francodichiera/dichiera-CartelLED/assets/ESP32+TIPS122 VERSION 3 TESTING/ESP32+TIPS/ESP32+TIPS (1).kicad_sch

## KiCad design assets/ESP32+TIPS122 VERSION 3 TESTING/ESP32+TIPS/ESP32+TIPS (1).kicad_sch (2025-08-08)

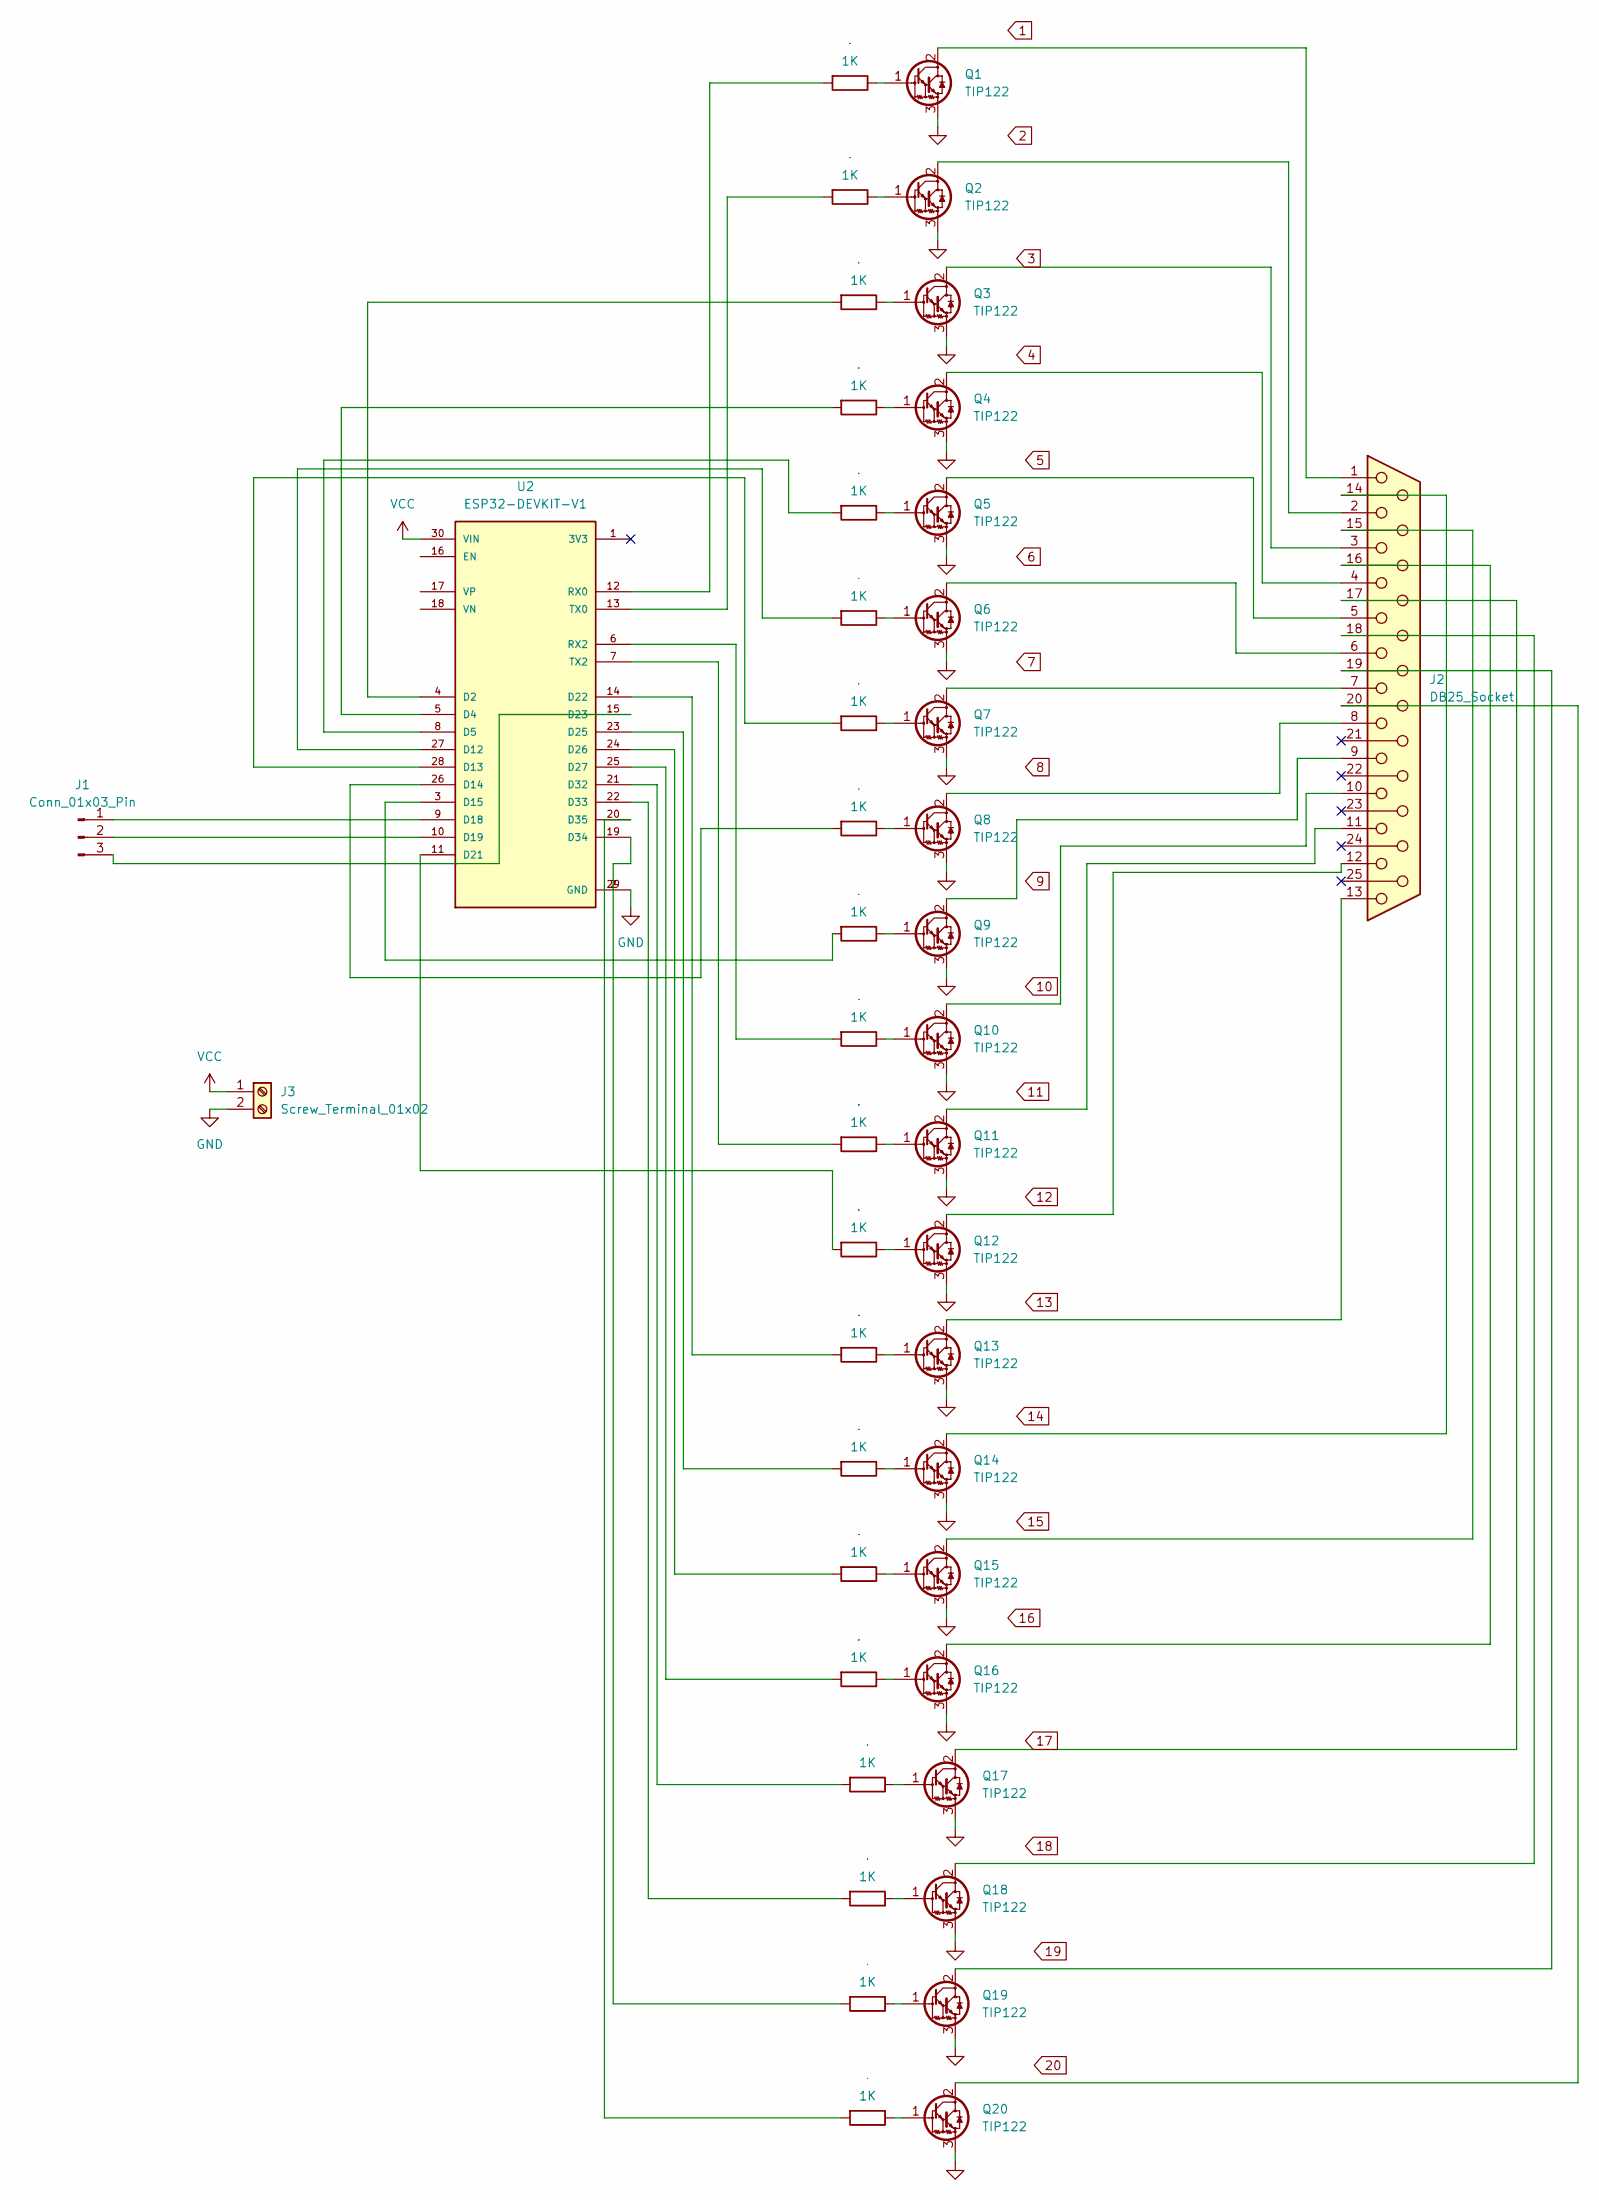
[picture p16: schematic ESP32+TIPS (1).kicad_sch]

Parts:
.1, .2, .3, .4, .5, .6, .7, .8, .9, .10, .11, .12, .13, .14, .15, .16, .17, .18, .19, .20: 1K; R_Axial_DIN0309_L9.0mm_D3.2mm_P20.32mm_Horizontal
J1: Conn_01x03_Pin; PinSocket_1x03_P2.54mm_Vertical
J2: DB25_Socket; DSUB-25_Pins_Horizontal_P2.77x2.54mm_EdgePinOffset9.40mm
J3: Screw_Terminal_01x02; TerminalBlock_Altech_AK300-2_P5.00mm
Q1, Q2, Q3, Q4, Q5, Q6, Q7, Q8, Q9, Q10, Q11, Q12, Q13, Q14, Q15, Q16, Q17, Q18, Q19, Q20: TIP122; TO-220-3_Vertical
U2: ESP32-DEVKIT-V1; MODULE_ESP32_DEVKIT_V1; PARTREV N/A

Connections:
GND: J3.2, Q1.3 (E), Q2.3 (E), Q3.3 (E), Q4.3 (E), Q5.3 (E), Q6.3 (E), Q7.3 (E), Q8.3 (E), Q9.3 (E), Q10.3 (E), Q11.3 (E), Q12.3 (E), Q13.3 (E), Q14.3 (E), Q15.3 (E), Q16.3 (E), Q17.3 (E), Q18.3 (E), Q19.3 (E), Q20.3 (E), U2.2 (GND), U2.29 (GND)
unnamed: .1.1, Q1.1 (B)
unnamed: .1.2, U2.12 (RX0)
unnamed: .2.1, Q2.1 (B)
unnamed: .2.2, U2.13 (TX0)
unnamed: .3.1, Q3.1 (B)
unnamed: .3.2, U2.4 (D2)
unnamed: .4.1, Q4.1 (B)
unnamed: .4.2, U2.5 (D4)
unnamed: .5.1, Q5.1 (B)
unnamed: .5.2, U2.8 (D5)
unnamed: .6.1, Q6.1 (B)
unnamed: .6.2, U2.27 (D12)
unnamed: .7.1, Q7.1 (B)
unnamed: .7.2, U2.28 (D13)
unnamed: .8.1, Q8.1 (B)
unnamed: .8.2, U2.26 (D14)
unnamed: .9.1, Q9.1 (B)
unnamed: .9.2, U2.3 (D15)
unnamed: .10.1, Q10.1 (B)
unnamed: .10.2, U2.6 (RX2)
unnamed: .11.1, Q11.1 (B)
unnamed: .11.2, U2.7 (TX2)
unnamed: .12.1, Q12.1 (B)
unnamed: .12.2, U2.11 (D21)
unnamed: .13.1, Q13.1 (B)
unnamed: .13.2, U2.14 (D22)
unnamed: .14.1, Q14.1 (B)
unnamed: .14.2, U2.23 (D25)
unnamed: .15.1, Q15.1 (B)
unnamed: .15.2, U2.24 (D26)
unnamed: .16.1, Q16.1 (B)
unnamed: .16.2, U2.25 (D27)
unnamed: .17.1, Q17.1 (B)
unnamed: .17.2, U2.21 (D32)
unnamed: .18.1, Q18.1 (B)
unnamed: .18.2, U2.22 (D33)
unnamed: .19.1, Q19.1 (B)
unnamed: .19.2, U2.19 (D34)
unnamed: .20.1, Q20.1 (B)
unnamed: .20.2, U2.20 (D35)
unnamed: J1.1, U2.9 (D18)
unnamed: J1.2, U2.10 (D19)
unnamed: J1.3, U2.15 (D23)
unnamed: J2.1, Q1.2 (C)
unnamed: J2.2, Q2.2 (C)
unnamed: J2.3, Q3.2 (C)
unnamed: J2.4, Q4.2 (C)
unnamed: J2.5, Q5.2 (C)
unnamed: J2.6, Q6.2 (C)
unnamed: J2.7, Q7.2 (C)
unnamed: J2.8, Q8.2 (C)
unnamed: J2.9, Q9.2 (C)
unnamed: J2.10, Q10.2 (C)
unnamed: J2.11, Q11.2 (C)
unnamed: J2.12, Q12.2 (C)
unnamed: J2.13, Q13.2 (C)
unnamed: J2.14, Q14.2 (C)
unnamed: J2.15, Q15.2 (C)
unnamed: J2.16, Q16.2 (C)
unnamed: J2.17, Q17.2 (C)
unnamed: J2.18, Q18.2 (C)
unnamed: J2.19, Q19.2 (C)
unnamed: J2.20, Q20.2 (C)
VCC: J3.1, U2.30 (VIN)
