francodichiera/dichiera-CartelLED/assets/Placa 74hc595 Version 2/74hc595/74hc595.kicad_sch

## KiCad design assets/Placa 74hc595 Version 2/74hc595/74hc595.kicad_sch (2025-08-04)

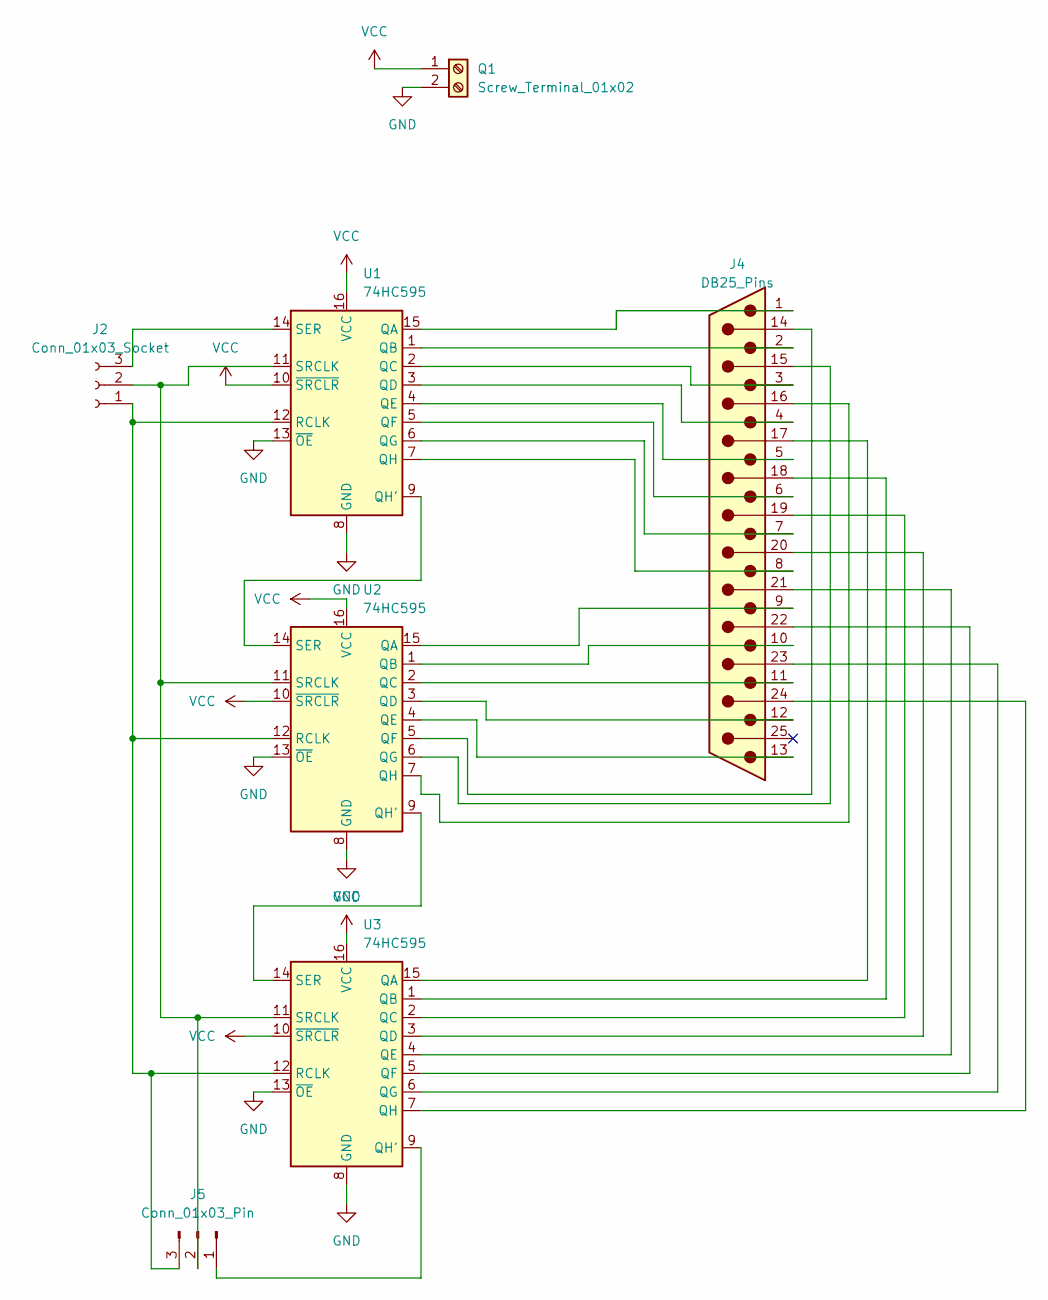
[picture p17: schematic 74hc595.kicad_sch]

Parts:
J2: Conn_01x03_Socket; PinHeader_1x03_P2.54mm_Vertical
J4: DB25_Pins; DSUB-25_Socket_Horizontal_P2.77x2.54mm_EdgePinOffset9.40mm
J5: Conn_01x03_Pin; PinHeader_1x03_P2.54mm_Vertical
Q1: Screw_Terminal_01x02; TerminalBlock_Altech_AK300-2_P5.00mm
U1, U2, U3: 74HC595; CERDIP-16_W7.62mm_SideBrazed_LongPads_Socket

Connections:
GND: Q1.2, U1.8 (GND), U1.13 (~OE), U2.8 (GND), U2.13 (~OE), U3.8 (GND), U3.13 (~OE)
unnamed: J2.1, J5.3, U1.12 (RCLK), U2.12 (RCLK), U3.12 (RCLK)
unnamed: J2.2, J5.2, U1.11 (SRCLK), U2.11 (SRCLK), U3.11 (SRCLK)
unnamed: J2.3, U1.14 (SER)
unnamed: J4.1, U1.15 (QA)
unnamed: J4.2, U1.1 (QB)
unnamed: J4.3, U1.2 (QC)
unnamed: J4.4, U1.3 (QD)
unnamed: J4.5, U1.4 (QE)
unnamed: J4.6, U1.5 (QF)
unnamed: J4.7, U1.6 (QG)
unnamed: J4.8, U1.7 (QH)
unnamed: J4.9, U2.15 (QA)
unnamed: J4.10, U2.1 (QB)
unnamed: J4.11, U2.2 (QC)
unnamed: J4.12, U2.3 (QD)
unnamed: J4.13, U2.4 (QE)
unnamed: J4.14, U2.5 (QF)
unnamed: J4.15, U2.6 (QG)
unnamed: J4.16, U2.7 (QH)
unnamed: J4.17, U3.15 (QA)
unnamed: J4.18, U3.1 (QB)
unnamed: J4.19, U3.2 (QC)
unnamed: J4.20, U3.3 (QD)
unnamed: J4.21, U3.4 (QE)
unnamed: J4.22, U3.5 (QF)
unnamed: J4.23, U3.6 (QG)
unnamed: J4.24, U3.7 (QH)
unnamed: J5.1, U3.9 (QH')
unnamed: U1.9 (QH'), U2.14 (SER)
unnamed: U2.9 (QH'), U3.14 (SER)
VCC: Q1.1, U1.10 (~SRCLR), U1.16 (VCC), U2.10 (~SRCLR), U2.16 (VCC), U3.10 (~SRCLR), U3.16 (VCC)
