francodichiera/dichiera-CartelLED/code/select_your_led/select_your_led.ino

#include <Arduino.h>
#include <ShiftRegister74HC595.h>  // https://blog.timodenk.com/shift-register-arduino-library/

/*Este código permite prender o apagar un solo LED específico usando coordenadas (x, y).*/

// === CONFIGURACIÓN DE PINES ===
#define DATA_PIN 23   // DS
#define CLOCK_PIN 18  // SHCP
#define LATCH_PIN 19  // STCP

#define MATRIX_ROWS 18
#define MATRIX_COLS 24

// Instancia del shift register (3 x 74HC595 = 24 salidas)
ShiftRegister74HC595<3> sr(DATA_PIN, CLOCK_PIN, LATCH_PIN);

// === Pines de filas conectadas a TIP122 ===
const uint8_t filas[MATRIX_ROWS] = {
  3, 1, 2, 4, 5,
  12, 13, 14, 15, 16,
  17, 21, 22, 25, 26,
  27, 32, 33
};

// === FUNCIONES ===
void prenderFila(uint8_t fila) {
  digitalWrite(filas[fila], HIGH);
}

void apagarFila(uint8_t fila) {
  digitalWrite(filas[fila], LOW);
}

void prenderLed(uint8_t x, uint8_t y) {
  if (x >= MATRIX_COLS || y >= MATRIX_ROWS)
    return;

  sr.set(x, HIGH);  // Activa columna X
  prenderFila(y);
}

void apagarLed(uint8_t x, uint8_t y) {
  if (x >= MATRIX_COLS || y >= MATRIX_ROWS)
    return;

  sr.set(x, LOW);
  apagarFila(y);
}

void setup() {
  Serial.begin(115200);

  // Configurar pines de filas como salidas
  for (int i = 0; i < MATRIX_ROWS; i++) {
    pinMode(filas[i], OUTPUT);
    apagarFila(i);
  }

  // Shift register ya se inicializa con la librería
  sr.setAllLow();  // Apaga todas las columnas
}

void loop() {
  prenderLed(0, 0);  // Prender LED en columna 5, fila 10
  delay(500);
  apagarLed(0, 0);  // Apagar el mismo LED
  delay(500);

  prenderLed(0, 17);  // Prender LED en columna 5, fila 10
  delay(500);
  apagarLed(0, 17);  // Apagar el mismo LED
  delay(500);

  prenderLed(23, 0);  // Prender LED en columna 5, fila 10
  delay(500);
  apagarLed(23, 0);  // Apagar el mismo LED
  delay(500);


  prenderLed(23, 17);  // Prender LED en columna 5, fila 10
  delay(500);
  apagarLed(23, 17);  // Apagar el mismo LED
  delay(500);
}
