francodichiera/dichiera-CartelLED/code/working_withServer/DS_DIGII11pt7b.h

#pragma once
#include <Adafruit_GFX.h>

const uint8_t DS_DIGII11pt7bBitmaps[] PROGMEM = {
  0x00, 0x25, 0x24, 0x80, 0x49, 0x24, 0x04, 0xB6, 0x80, 0x02, 0x04, 0x81,
  0x20, 0x48, 0xED, 0x8D, 0x83, 0x63, 0x26, 0xCD, 0x8D, 0x02, 0x40, 0x90,
  0x04, 0x01, 0x00, 0x40, 0xFF, 0x00, 0x10, 0x04, 0x01, 0x00, 0x40, 0x0F,
  0xC0, 0x08, 0x02, 0x00, 0x80, 0x20, 0x08, 0x04, 0xFE, 0x06, 0x01, 0x80,
  0x00, 0x30, 0x47, 0x1B, 0x26, 0x64, 0x88, 0xB0, 0xEC, 0x00, 0x00, 0x40,
  0x1B, 0x82, 0xC8, 0xD9, 0x33, 0x24, 0x44, 0x87, 0x00, 0x3F, 0x10, 0x04,
  0x01, 0x00, 0x40, 0x90, 0x67, 0xFC, 0x00, 0x80, 0xA0, 0x48, 0x12, 0x04,
  0x81, 0x1F, 0x80, 0xE0, 0x18, 0x04, 0x10, 0x41, 0x00, 0x00, 0x41, 0x08,
  0x20, 0x81, 0xC0, 0x38, 0x02, 0x10, 0x84, 0x21, 0x08, 0x42, 0x20, 0x30,
  0x10, 0x4D, 0x5B, 0xDF, 0xF3, 0x00, 0x10, 0x23, 0xF8, 0x03, 0x06, 0x04,
  0x00, 0xE0, 0xFC, 0xC0, 0x00, 0x80, 0x80, 0xC0, 0x40, 0x40, 0x60, 0x00,
  0x20, 0x20, 0x10, 0x10, 0x10, 0x08, 0x00, 0x3F, 0x90, 0x24, 0x09, 0x02,
  0x40, 0x90, 0x20, 0x08, 0x02, 0x40, 0x90, 0x28, 0x0A, 0x02, 0x81, 0x0F,
  0xC0, 0x5A, 0xA0, 0xAA, 0x80, 0x3F, 0x80, 0x20, 0x08, 0x02, 0x00, 0x80,
  0x23, 0xF8, 0x00, 0x40, 0x10, 0x08, 0x02, 0x00, 0x80, 0x1F, 0xC0, 0x3F,
  0x80, 0x20, 0x08, 0x02, 0x00, 0x80, 0x23, 0xF8, 0x02, 0x00, 0x80, 0x20,
  0x08, 0x02, 0x01, 0x1F, 0x80, 0x80, 0x40, 0xA0, 0x50, 0x28, 0x14, 0x09,
  0xFC, 0x02, 0x01, 0x00, 0x80, 0x40, 0x20, 0x20, 0x3F, 0xA0, 0x10, 0x08,
  0x04, 0x02, 0x00, 0xFC, 0x00, 0x00, 0x80, 0x40, 0x20, 0x10, 0x13, 0xF0,
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
  {   445,  10,  13,  11,    1,  -13 },   // 0x46 'F'
  {   462,   9,  14,  11,    1,  -13 },   // 0x47 'G'
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

const GFXfont DS_DIGII11pt7b PROGMEM = {
  (uint8_t  *)DS_DIGII11pt7bBitmaps,
  (GFXglyph *)DS_DIGII11pt7bGlyphs,
  0x20, 0x7E, 22 };

// Approx. 1949 bytes
