francodichiera/dichiera-CartelLED/code/working_withServer/LEMONMILK_Regular10pt7b.h

#pragma once
#include <Adafruit_GFX.h>

const uint8_t LEMONMILK_Regular10pt7bBitmaps[] PROGMEM = {
  0x00, 0x6D, 0xB6, 0xDB, 0x6C, 0x01, 0xFF, 0xDF, 0x6D, 0xB2, 0xC8, 0x18,
  0x60, 0xC3, 0x06, 0x18, 0x30, 0xC1, 0x86, 0x7F, 0xFF, 0xFF, 0xE3, 0x18,
  0x10, 0xC1, 0x86, 0x3F, 0xFD, 0xFF, 0xE3, 0x0C, 0x18, 0xC0, 0xC6, 0x06,
  0x30, 0x06, 0x00, 0xC0, 0x7E, 0x1F, 0xE7, 0x6C, 0xCC, 0x19, 0x83, 0xB0,
  0x3E, 0x03, 0xF0, 0x1F, 0x03, 0xF0, 0x66, 0x0C, 0xD9, 0x9B, 0xFF, 0x7F,
  0xC3, 0xF0, 0x18, 0x03, 0x00, 0x38, 0x18, 0xF8, 0x23, 0xB8, 0xC6, 0x33,
  0x0C, 0x64, 0x1D, 0xD8, 0x1F, 0x20, 0x1C, 0xC0, 0x03, 0x00, 0x04, 0x70,
  0x19, 0xF0, 0x66, 0x30, 0xCC, 0x63, 0x18, 0xC4, 0x1F, 0x18, 0x1C, 0x0F,
  0x00, 0x7E, 0x03, 0x9C, 0x0C, 0x20, 0x30, 0x00, 0xC0, 0x03, 0x80, 0x0F,
  0x00, 0x7E, 0x33, 0xB8, 0xCC, 0x7B, 0x30, 0xFC, 0xC1, 0xE1, 0x87, 0xC7,
  0xFF, 0xC7, 0xC3, 0xFF, 0xC0, 0x33, 0x98, 0xCE, 0x63, 0x18, 0xC6, 0x31,
  0x8C, 0x71, 0x8C, 0x31, 0x80, 0x63, 0x8C, 0x63, 0x8C, 0x63, 0x18, 0xC6,
  0x31, 0x98, 0xC6, 0x63, 0x00, 0x32, 0xDF, 0xCC, 0xFE, 0xD3, 0x00, 0x0C,
  0x06, 0x03, 0x01, 0x8F, 0xFF, 0xFC, 0x30, 0x18, 0x0C, 0x06, 0x00, 0x6F,
  0x73, 0x26, 0xFF, 0xFF, 0xFF, 0x80, 0x03, 0x01, 0x80, 0xC0, 0xC0, 0x60,
  0x30, 0x30, 0x18, 0x1C, 0x0C, 0x06, 0x07, 0x03, 0x01, 0x81, 0xC0, 0xC0,
  0x60, 0x70, 0x00, 0x0F, 0x03, 0xFC, 0x70, 0xE6, 0x06, 0x60, 0x6C, 0x03,
  0xC0, 0x3C, 0x03, 0xC0, 0x3C, 0x03, 0xC0, 0x3E, 0x06, 0x60, 0x67, 0x0E,
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
  {   632,   9,  16,  11,    1,  -15 },   // 0x46 'F'
  {   650,  15,  16,  17,    1,  -15 },   // 0x47 'G'
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

const GFXfont LEMONMILK_Regular10pt7b PROGMEM = {
  (uint8_t  *)LEMONMILK_Regular10pt7bBitmaps,
  (GFXglyph *)LEMONMILK_Regular10pt7bGlyphs,
  0x20, 0x7E, 26 };

// Approx. 2519 bytes
