francodichiera/dichiera-CartelLED/code/working_withServer/LEMONMILK_Regular11pt7b.h

#pragma once
#include <Adafruit_GFX.h>

const uint8_t LEMONMILK_Regular11pt7bBitmaps[] PROGMEM = {
  0x00, 0xFF, 0xFF, 0xFF, 0xFF, 0x80, 0x07, 0xE0, 0xCF, 0x3C, 0xF3, 0xCC,
  0x0C, 0x30, 0x30, 0xC0, 0xC3, 0x03, 0x0C, 0x1C, 0x31, 0xFF, 0xFF, 0xFF,
  0xC6, 0x18, 0x18, 0x60, 0x61, 0x81, 0x86, 0x3F, 0xFF, 0xFF, 0xF8, 0xC3,
  0x83, 0x0C, 0x0C, 0x30, 0x30, 0xC0, 0x06, 0x00, 0x60, 0x1F, 0x83, 0xFE,
  0x7F, 0xE7, 0x64, 0x76, 0x07, 0x60, 0x3E, 0x01, 0xF0, 0x0F, 0xC0, 0x7E,
  0x06, 0xF0, 0x67, 0x26, 0x7E, 0x6F, 0x7F, 0xE3, 0xFC, 0x1F, 0x80, 0x60,
  0x06, 0x00, 0x3C, 0x06, 0x33, 0x06, 0x30, 0xC7, 0x18, 0x63, 0x0C, 0x33,
  0x03, 0x33, 0x80, 0xF1, 0x80, 0x01, 0x80, 0x01, 0xC0, 0x00, 0xC0, 0x00,
  0xC7, 0x80, 0xC6, 0x60, 0x66, 0x18, 0x63, 0x0C, 0x61, 0x86, 0x30, 0x66,
  0x30, 0x1E, 0x00, 0x0F, 0x00, 0x3F, 0x00, 0xF7, 0x01, 0xC6, 0x03, 0x80,
  0x07, 0x00, 0x07, 0x00, 0x0E, 0x00, 0x3E, 0x00, 0xEC, 0x73, 0x9C, 0xE7,
  0x1D, 0xCE, 0x1F, 0x1C, 0x1E, 0x1C, 0x3E, 0x1F, 0xFF, 0x1F, 0x0E, 0xDB,
  0x6C, 0x18, 0xE3, 0x1C, 0x73, 0x8E, 0x38, 0xE3, 0x8E, 0x38, 0xE3, 0xC7,
  0x1C, 0x38, 0xE1, 0xC0, 0x61, 0xC3, 0x0E, 0x38, 0x71, 0xC7, 0x1C, 0x71,
  0xC7, 0x1C, 0xE3, 0x8E, 0x71, 0xCE, 0x00, 0x10, 0x23, 0x5B, 0xC3, 0x9A,
  0xC4, 0x08, 0x0E, 0x03, 0x80, 0xE0, 0x38, 0xFF, 0xFF, 0xF0, 0xE0, 0x38,
  0x0E, 0x03, 0x80, 0xE0, 0xEF, 0x33, 0x60, 0xFF, 0xFF, 0xFC, 0x01, 0x80,
  0xC0, 0xE0, 0x60, 0x70, 0x30, 0x18, 0x1C, 0x0C, 0x06, 0x07, 0x03, 0x01,
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
  {   763,  10,  17,  13,    2,  -16 },   // 0x46 'F'
  {   785,  17,  17,  19,    1,  -16 },   // 0x47 'G'
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

const GFXfont LEMONMILK_Regular11pt7b PROGMEM = {
  (uint8_t  *)LEMONMILK_Regular11pt7bBitmaps,
  (GFXglyph *)LEMONMILK_Regular11pt7bGlyphs,
  0x20, 0x7E, 29 };

// Approx. 2916 bytes
