francodichiera/dichiera-CartelLED/code/working_withServer/FreeSans10pt7b.h

#pragma once
#include <Adafruit_GFX.h>

const uint8_t FreeSans10pt7bBitmaps[] PROGMEM = {
  0x00, 0xFF, 0xFD, 0x54, 0xF0, 0xDE, 0xF7, 0xB8, 0x80, 0x0C, 0x81, 0x10,
  0x22, 0x04, 0xC7, 0xFE, 0xFF, 0xC4, 0x40, 0x88, 0x11, 0x1F, 0xF8, 0xCC,
  0x19, 0x02, 0x20, 0x44, 0x00, 0x08, 0x1F, 0x1A, 0xD9, 0x38, 0x9E, 0x43,
  0x20, 0xF8, 0x1F, 0x05, 0xC2, 0x71, 0x18, 0x9E, 0x4D, 0xFC, 0x10, 0x08,
  0x00, 0x00, 0x10, 0x78, 0x20, 0xCC, 0x20, 0x84, 0x40, 0x84, 0x40, 0xCC,
  0x80, 0x79, 0x80, 0x01, 0x00, 0x03, 0x3E, 0x02, 0x62, 0x06, 0x63, 0x04,
  0x63, 0x0C, 0x62, 0x08, 0x3E, 0x1E, 0x07, 0xE0, 0x8C, 0x10, 0x83, 0x30,
  0x3C, 0x07, 0x01, 0xE2, 0x66, 0x58, 0x7B, 0x06, 0x60, 0xCE, 0x3C, 0xFC,
  0xC0, 0xFF, 0x80, 0x11, 0x88, 0x46, 0x21, 0x18, 0xC6, 0x10, 0x84, 0x30,
  0x84, 0x10, 0x80, 0x84, 0x62, 0x23, 0x33, 0x33, 0x33, 0x32, 0x64, 0x48,
  0x22, 0xAF, 0x9C, 0x58, 0x08, 0x04, 0x02, 0x01, 0x0F, 0xF8, 0x40, 0x20,
  0x10, 0x08, 0x00, 0xF5, 0x80, 0xF8, 0xF0, 0x08, 0x20, 0x84, 0x10, 0x42,
  0x08, 0x21, 0x04, 0x10, 0xC2, 0x00, 0x1C, 0x3F, 0x18, 0xD8, 0x2C, 0x1E,
  0x0F, 0x07, 0x83, 0xC1, 0xE0, 0xF0, 0x78, 0x26, 0x31, 0xF0, 0x08, 0xCF,
  0xF1, 0x8C, 0x63, 0x18, 0xC6, 0x31, 0x8C, 0x3E, 0x3F, 0xB0, 0x78, 0x3C,
  0x18, 0x0C, 0x0C, 0x1C, 0x1C, 0x38, 0x18, 0x18, 0x0F, 0xFF, 0xFC, 0x3C,
  0x3F, 0xB0, 0xD8, 0x2C, 0x10, 0x18, 0x78, 0x3E, 0x01, 0x80, 0xE0, 0x78,
  0x3E, 0x33, 0xF0, 0x02, 0x03, 0x03, 0x83, 0xC1, 0x61, 0xB1, 0x98, 0x8C,
  0xC6, 0x7F, 0xFF, 0xE0, 0xC0, 0x60, 0x30, 0x7F, 0x3F, 0x90, 0x08, 0x04,
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
  {   499,   9,  14,  12,    2,  -13 },   // 0x46 'F'
  {   515,  13,  15,  15,    1,  -14 },   // 0x47 'G'
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

const GFXfont FreeSans10pt7b PROGMEM = {
  (uint8_t  *)FreeSans10pt7bBitmaps,
  (GFXglyph *)FreeSans10pt7bGlyphs,
  0x20, 0x7E, 33 };

// Approx. 1996 bytes
