francodichiera/dichiera-CartelLED/code/working_withServer/FreeSans11pt7b.h

#pragma once
#include <Adafruit_GFX.h>

const uint8_t FreeSans11pt7bBitmaps[] PROGMEM = {
  0x00, 0xFF, 0xF3, 0xCF, 0x3C, 0xB2, 0x48, 0x0C, 0x40, 0xC4, 0x0C, 0xC0,
  0x8C, 0x7F, 0xF7, 0xFF, 0x18, 0x81, 0x98, 0x19, 0x8F, 0xFE, 0xFF, 0xE3,
  0x10, 0x31, 0x03, 0x30, 0x23, 0x00, 0x0C, 0x03, 0x03, 0xF1, 0xB6, 0xCC,
  0xF3, 0x3C, 0xC3, 0xB0, 0x7C, 0x0F, 0xC0, 0xF8, 0x33, 0x0C, 0xF3, 0x3C,
  0xCF, 0xB6, 0x7F, 0x83, 0x00, 0xC0, 0x30, 0x38, 0x08, 0x1F, 0x06, 0x0C,
  0x61, 0x02, 0x18, 0x80, 0x86, 0x20, 0x31, 0x90, 0x07, 0xCC, 0x00, 0xC2,
  0x00, 0x01, 0x8F, 0x00, 0x47, 0xE0, 0x33, 0x08, 0x08, 0xC3, 0x06, 0x30,
  0x81, 0x06, 0x60, 0xC1, 0xF0, 0x1F, 0x01, 0x9C, 0x0C, 0x60, 0x63, 0x03,
  0x18, 0x0F, 0x80, 0x38, 0x07, 0xC0, 0x66, 0x26, 0x1B, 0x30, 0x79, 0x81,
  0x8C, 0x0E, 0x31, 0xF8, 0xFC, 0xC0, 0x00, 0xFF, 0x40, 0x13, 0x26, 0x4C,
  0xCC, 0x88, 0x88, 0x8C, 0xCC, 0x46, 0x23, 0x10, 0x82, 0x10, 0xC2, 0x18,
  0xC2, 0x10, 0x86, 0x21, 0x08, 0xC6, 0x23, 0x11, 0x88, 0x00, 0x30, 0x4D,
  0xDE, 0x39, 0x20, 0x00, 0x04, 0x00, 0x80, 0x10, 0x02, 0x0F, 0xFF, 0xFF,
  0xC1, 0x00, 0x20, 0x04, 0x00, 0x80, 0xF5, 0xC0, 0xFF, 0xC0, 0xF0, 0x04,
  0x10, 0x82, 0x08, 0x41, 0x04, 0x30, 0x82, 0x18, 0x41, 0x0C, 0x20, 0x3F,
  0x1C, 0xE6, 0x1B, 0x06, 0xC0, 0xF0, 0x3C, 0x0F, 0x03, 0xC0, 0xF0, 0x3C,
  0x0F, 0x03, 0x61, 0x9C, 0xE3, 0xF0, 0x00, 0x08, 0xCF, 0xF0, 0x84, 0x21,
  0x08, 0x42, 0x10, 0x84, 0x20, 0x3F, 0x1C, 0xE6, 0x0F, 0x03, 0xC0, 0xC0,
  0x30, 0x18, 0x0E, 0x0E, 0x0F, 0x07, 0x01, 0x80, 0xC0, 0x3F, 0xFF, 0xFC,
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
  {   604,  10,  16,  13,    2,  -15 },   // 0x46 'F'
  {   624,  14,  17,  17,    1,  -15 },   // 0x47 'G'
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

const GFXfont FreeSans11pt7b PROGMEM = {
  (uint8_t  *)FreeSans11pt7bBitmaps,
  (GFXglyph *)FreeSans11pt7bGlyphs,
  0x20, 0x7E, 36 };

// Approx. 2294 bytes
